dhruxraj/stm32-can-ecu/hardware/gen/fab.py

"""
fab.py - fabrication outputs generated WITHOUT KiCad:
  hardware/fab/gerber/*.g??   RS-274X Gerbers (X2 file attributes), planes and
                              pours included (solid pad connection, no thermals)
  hardware/fab/drill/*.drl     Excellon, separate PTH / NPTH
  hardware/fab/BOM.csv         grouped bill of materials with cost ESTIMATES
  hardware/fab/CPL_top.csv     pick-and-place (top side)
These are PREVIEW outputs for review.  For ordering, re-plot from KiCad
(File > Fabrication Outputs) after filling zones - see docs/MANUFACTURING.md.
"""
import csv
import json
import math
import os
import re

import matplotlib
matplotlib.use("Agg")
import matplotlib.pyplot as plt
from matplotlib.patches import Polygon as MPoly, Circle
from matplotlib.textpath import TextPath
from matplotlib.font_manager import FontProperties

from board import placed_pads_cache, PLACEMENT, outline_polygon, BX1, BY1, BX2, BY2, FOOTPRINTS
from design import PARTS
from lib import rot_pt

ROOT = "/home/claude/stm32-can-ecu/hardware/fab"
GEN = "/home/claude/stm32-can-ecu/hardware/gen"
ZONE_CLR = 0.25
MASK_EXP = 0.05


def gy(y):
    return -y


def c6(v):
    return str(int(round(v * 1e6)))


class Gerber:
    def __init__(self, func, polarity="Positive"):
        self.lines = ["G04 STM32 CAN ECU rev A - generated by hardware/gen/fab.py*",
                      "%TF.GenerationSoftware,custom,can-ecu-gen,1.0*%",
                      "%TF.ProjectId,CAN_ECU,00000000-0000-0000-0000-000000000000,A*%",
                      f"%TF.FileFunction,{func}*%", f"%TF.FilePolarity,{polarity}*%",
                      "%FSLAX46Y46*%", "%MOMM*%", "%LPD*%", "G01*"]
        self.aps = {}
        self.body = []
        self.cur_ap = None
        self.pol = "D"

    def ap(self, kind, *dims):
        key = (kind,) + tuple(round(d, 4) for d in dims)
        if key not in self.aps:
            n = 10 + len(self.aps)
            self.aps[key] = n
        return self.aps[key]

    def _sel(self, n):
        if self.cur_ap != n:
            self.body.append(f"D{n}*")
            self.cur_ap = n

    def polarity(self, p):
        if p != self.pol:
            self.body.append(f"%LP{p}*%")
            self.pol = p

    def flash_circle(self, x, y, d):
        self._sel(self.ap("C", d))
        self.body.append(f"X{c6(x)}Y{c6(gy(y))}D03*")

    def flash_rect(self, x, y, w, h):
        self._sel(self.ap("R", w, h))
        self.body.append(f"X{c6(x)}Y{c6(gy(y))}D03*")

    def flash_obround(self, x, y, w, h):
        self._sel(self.ap("O", w, h))
        self.body.append(f"X{c6(x)}Y{c6(gy(y))}D03*")

    def line(self, a, b, w):
        self._sel(self.ap("C", w))
        self.body.append(f"X{c6(a[0])}Y{c6(gy(a[1]))}D02*")
        self.body.append(f"X{c6(b[0])}Y{c6(gy(b[1]))}D01*")

    def region(self, pts):
        self.body.append("G36*")
        self.body.append(f"X{c6(pts[0][0])}Y{c6(gy(pts[0][1]))}D02*")
        for p in pts[1:] + [pts[0]]:
            self.body.append(f"X{c6(p[0])}Y{c6(gy(p[1]))}D01*")
        self.body.append("G37*")

    def save(self, path):
        out = list(self.lines)
        for key, n in sorted(self.aps.items(), key=lambda x: x[1]):
            kind = key[0]
            if kind == "C":
                out.append(f"%ADD{n}C,{key[1]:.4f}*%")
            elif kind == "R":
                out.append(f"%ADD{n}R,{key[1]:.4f}X{key[2]:.4f}*%")
            elif kind == "O":
                out.append(f"%ADD{n}O,{key[1]:.4f}X{key[2]:.4f}*%")
        out += self.body
        if self.pol != "D":
            out.append("%LPD*%")
        out.append("M02*")
        open(path, "w").write("\n".join(out) + "\n")


def rounded_rect_pts(cx, cy, w, h, r, rot, n=4):
    """polygon of a (rounded) rectangle, rotation multiple of 90."""
    if rot % 180 == 90:
        w, h = h, w
    r = min(r, w / 2, h / 2)
    pts = []
    corners = [(cx + w / 2 - r, cy - h / 2 + r, -90, 0), (cx + w / 2 - r, cy + h / 2 - r, 0, 90),
               (cx - w / 2 + r, cy + h / 2 - r, 90, 180), (cx - w / 2 + r, cy - h / 2 + r, 180, 270)]
    for x, y, a0, a1 in corners:
        if r <= 1e-6:
            pts.append((x, y))
            continue
        for i in range(n + 1):
            a = math.radians(a0 + (a1 - a0) * i / n)
            pts.append((x + r * math.cos(a), y + r * math.sin(a)))
    return pts


def draw_pad(g, p, grow=0.0):
    """draw pad copper (optionally grown by `grow`) with the current polarity."""
    w, h = p.w + 2 * grow, p.h + 2 * grow
    if p.shape == "circle":
        g.flash_circle(p.x, p.y, w)
    elif p.shape == "oval":
        if p.rot % 180 == 90:
            w, h = h, w
        g.flash_obround(p.x, p.y, w, h)
    elif p.shape == "rect" and grow == 0:
        if p.rot % 180 == 90:
            w, h = h, w
        g.flash_rect(p.x, p.y, w, h)
    else:
        r = (min(p.w, p.h) * p.pad.rratio if p.shape == "roundrect" else 0.0) + grow
        g.region(rounded_rect_pts(p.x, p.y, w, h, r, p.rot))


def load_routes():
    return json.load(open(os.path.join(GEN, "routes.json")))


def copper_layer(layer, R, pour_net=None, plane=False):
    func = {"F.Cu": "Copper,L1,Top", "In1.Cu": "Copper,L2,Inr", "In2.Cu": "Copper,L3,Inr",
            "B.Cu": "Copper,L4,Bot"}[layer]
    g = Gerber(func)
    pads = [p for p in placed_pads_cache() if layer in p.layers]
    tracks = [t for t in R["tracks"] if t["layer"] == layer]
    vias = R["vias"]
    npth = [p for p in placed_pads_cache() if p.kind == "np_thru_hole"]
    if pour_net:
        g.region(outline_polygon(0.3, 8))
        g.polarity("C")
        for p in pads:
            if p.net != pour_net:
                draw_pad(g, p, ZONE_CLR)
        for t in tracks:
            if t["net"] != pour_net:
                g.line(t["a"], t["b"], t["w"] + 2 * ZONE_CLR)
        for v in vias:
            if v["net"] != pour_net:
                g.flash_circle(v["at"][0], v["at"][1], v["size"] + 2 * ZONE_CLR)
        for p in npth:
            g.flash_circle(p.x, p.y, p.drill + 2 * 0.5)
        g.polarity("D")
    if not plane:
        for t in tracks:
            g.line(t["a"], t["b"], t["w"])
    for p in pads:
        if plane and p.net != pour_net:
            continue            # inner layers: non-plane pads have no copper (unused pads removed)
        draw_pad(g, p)
    for v in vias:
        if plane and v["net"] != pour_net:
            continue
        g.flash_circle(v["at"][0], v["at"][1], v["size"])
    return g


def mask_layer(side, R):
    g = Gerber("Soldermask,Top" if side == "F" else "Soldermask,Bot", "Negative")
    for p in placed_pads_cache():
        if p.kind == "np_thru_hole":
            g.flash_circle(p.x, p.y, p.drill + 0.1)
            continue
        if side == "B" and p.kind != "thru_hole":
            continue
        draw_pad(g, p, MASK_EXP)
    return g            # vias are tented


def paste_layer(R):
    g = Gerber("Paste,Top", "Positive")
    for p in placed_pads_cache():
        if p.kind == "smd":
            draw_pad(g, p)
    return g


FONT = FontProperties(family="DejaVu Sans")


def text_polys(s, x, y, size, rot):
    tp = TextPath((0, 0), s, size=size * 1.35, prop=FONT)
    polys = tp.to_polygons()
    if not polys:
        return []
    xs = [p[0] for poly in polys for p in poly]
    ys = [p[1] for poly in polys for p in poly]
    cx, cy = (min(xs) + max(xs)) / 2, (min(ys) + max(ys)) / 2
    out = []
    for poly in polys:
        pts = []
        for (px, py) in poly:
            lx, ly = px - cx, -(py - cy)          # text y-up -> board y-down
            dx, dy = rot_pt(lx, ly, rot)
            pts.append((x + dx, y + dy))
        area = sum(pts[i][0] * pts[(i + 1) % len(pts)][1] - pts[(i + 1) % len(pts)][0] * pts[i][1]
                   for i in range(len(pts))) / 2
        out.append((pts, area))
    return out


def silk_layer(meta):
    from write_kicad import BOARD_TEXT
    g = Gerber("Legend,Top")
    pads = placed_pads_cache()
    for ref, part in PARTS.items():
        fx, fy, frot = PLACEMENT[ref]
        f = FOOTPRINTS[part.fp]
        for gr in f.gfx:
            if gr[1] != "F.SilkS":
                continue
            if gr[0] == "line":
                _, L, x1, y1, x2, y2, w = gr
                a = rot_pt(x1, y1, frot); b = rot_pt(x2, y2, frot)
                g.line((fx + a[0], fy + a[1]), (fx + b[0], fy + b[1]), w)
            else:
                _, L, cx, cy, r, w = gr
                c = rot_pt(cx, cy, frot)
                n = 36
                pts = [(fx + c[0] + r * math.cos(2 * math.pi * i / n), fy + c[1] + r * math.sin(2 * math.pi * i / n))
                       for i in range(n + 1)]
                for a, b in zip(pts[:-1], pts[1:]):
                    g.line(a, b, w)
    texts = []
    for ref, s in meta["silk"].items():
        if s:
            texts.append((ref, s[0], s[1], 0.8, s[2]))
    for (t, x, y, sz, rot) in BOARD_TEXT:
        texts.append((t, x, y, sz, rot))
    for (t, x, y, sz, rot) in texts:
        polys = text_polys(t, x, y, sz, rot)
        # matplotlib glyph outer contours come out with positive area in board
        # (y-down) coordinates, counter/hole contours negative
        outer = [p for p, a in polys if a > 0]
        holes = [p for p, a in polys if a <= 0]
        for p in outer:
            g.region(p)
            for a, b in zip(p, p[1:] + p[:1]):      # embolden: KiCad plots 0.15 mm strokes
                g.line(a, b, 0.07)
        if holes:
            g.polarity("C")
            for p in holes:
                g.region(p)
            g.polarity("D")
    # clip silk from exposed pads (as KiCad does)
    g.polarity("C")
    for p in pads:
        if p.kind != "np_thru_hole":
            draw_pad(g, p, MASK_EXP + 0.05)
    g.polarity("D")
    return g


def edge_layer():
    g = Gerber("Profile,NP")
    pts = outline_polygon(0.0, 16)
    for a, b in zip(pts, pts[1:] + pts[:1]):
        g.line(a, b, 0.1)
    return g


def drill_files(R, d):
    pth, npth = {}, {}
    for p in placed_pads_cache():
        if p.drill:
            (npth if p.kind == "np_thru_hole" else pth).setdefault(p.drill, []).append((p.x, p.y))
    for v in R["vias"]:
        pth.setdefault(v["drill"], []).append(tuple(v["at"]))
    for name, tools, plated in [("CAN_ECU-PTH.drl", pth, True), ("CAN_ECU-NPTH.drl", npth, False)]:
        out = ["M48", "; DRILL file - STM32 CAN ECU rev A - generated by hardware/gen/fab.py",
               f"; #@! TF.FileFunction,{'Plated,1,4,PTH' if plated else 'NonPlated,1,4,NPTH'}",
               "FMAT,2", "METRIC,TZ"]
        tl = sorted(tools)
        for i, dia in enumerate(tl):
            out.append(f"T{i + 1}C{dia:.3f}")
        out += ["%", "G90", "G05"]
        for i, dia in enumerate(tl):
            out.append(f"T{i + 1}")
            for x, y in tools[dia]:
                out.append(f"X{x:.3f}Y{gy(y):.3f}")
        out += ["T0", "M30"]
        open(os.path.join(d, name), "w").write("\n".join(out) + "\n")
    return pth, npth


# ------------------------------------------------------------------ BOM / CPL
COST = [  # (match on MPN/value substring, est. unit cost USD at qty 10) - ROUGH estimates only
    ("STM32G431CBT6", 4.60), ("TJA1051T", 1.10), ("LSM6DS3TR-C", 2.40), ("R-78E5.0", 3.60),
    ("AP2112K", 0.35), ("SMBJ18A", 0.25), ("SS34", 0.15), ("PTC", 0.35), ("PESD1CAN", 0.25),
    ("8MHz", 0.40), ("1729128", 0.70), ("1729131", 1.00), ("1x6", 0.25), ("2x5", 0.35),
    ("2x2", 0.30), ("tactile", 0.15), ("47uF", 0.20), ("10uF 50V", 0.35), ("10uF", 0.08),
    ("4.7uF", 0.06), ("1uF", 0.03), ("60R4", 0.04), ("LED", 0.05), ("600R", 0.05),
    ("15pF", 0.03), ("4.7nF", 0.03), ("100nF", 0.02), ("R", 0.01),
]


def est_cost(p):
    key = f"{p.mpn} {p.value} {p.sym}"
    for k, c in COST:
        if k in key:
            return c
    return 0.0


def bom(d):
    groups = {}
    for p in PARTS.values():
        if p.sym in ("MountingHole", "TestPoint", "SolderJumper_2_Open"):
            continue
        k = (p.value, p.fp, p.mpn)
        groups.setdefault(k, []).append(p)
    rows = []
    total = 0.0
    for i, ((val, fp, mpn), ps) in enumerate(sorted(groups.items(), key=lambda x: _refkey(x[1][0].ref))):
        refs = sorted((p.ref for p in ps), key=_refkey)
        uc = est_cost(ps[0])
        total += uc * len(ps)
        f = FOOTPRINTS[fp]
        descs = "; ".join(sorted({p.desc for p in ps}))
        spec = mpn or f"generic {val}, {fp.split('_')[1] if fp[:2] in ('R_', 'C_', 'L_') else fp}"
        rows.append([i + 1, len(ps), " ".join(refs), val, fp, f.std, spec, ps[0].mfr, descs,
                     "THT" if f.attr == "through_hole" else "SMD", f"{uc:.2f}", f"{uc * len(ps):.2f}"])
    with open(os.path.join(d, "BOM.csv"), "w", newline="") as fh:
        w = csv.writer(fh)
        w.writerow(["Item", "Qty", "References", "Value", "Footprint (project lib)", "Equivalent KiCad std footprint",
                    "MPN / specification", "Manufacturer", "Description", "Mount", "Est. unit USD", "Est. ext. USD"])
        w.writerows(rows)
        w.writerow([])
        w.writerow(["", "", "", "", "", "", "", "", "Estimated component total per board (qty-10 pricing, "
                    "ROUGH ESTIMATE - check distributor)", "", "", f"{total:.2f}"])
        w.writerow(["", "", "JP1 JP3 JP4", "Solder jumpers", "", "", "PCB feature - no part", "", "", "", "", ""])
        w.writerow(["", "", "TP1-TP8", "Test pads", "", "", "PCB feature - no part", "", "", "", "", ""])
        w.writerow(["", "", "H1-H4", "M3 mounting holes", "", "", "PCB feature - no part", "", "", "", "", ""])
    return rows, total


def _refkey(r):
    m = re.match(r"([A-Z]+)(\d+)", r)
    return (m.group(1), int(m.group(2)))


def cpl(d):
    with open(os.path.join(d, "CPL_top.csv"), "w", newline="") as fh:
        w = csv.writer(fh)
        w.writerow(["Designator", "Mid X (mm)", "Mid Y (mm)", "Rotation (deg, CCW)", "Layer", "Mount", "Value",
                    "Footprint"])
        for ref in sorted(PARTS, key=_refkey):
            p = PARTS[ref]
            f = FOOTPRINTS[p.fp]
            if f.attr == "exclude" or p.sym in ("TestPoint", "SolderJumper_2_Open"):
                continue
            x, y, r = PLACEMENT[ref]
            w.writerow([ref, f"{x - BX1:.3f}", f"{BY2 - y:.3f}", r, "Top",
                        "THT" if f.attr == "through_hole" else "SMD", p.value, p.fp])


# ------------------------------------------------------------------ gerber re-render (independent check)
def render_gerber(path, ax, color, bg):
    txt = open(path).read()
    aps = {}
    for m in re.finditer(r"%ADD(\d+)([CRO]),([\d.]+)(?:X([\d.]+))?\*%", txt):
        aps[int(m.group(1))] = (m.group(2), float(m.group(3)), float(m.group(4) or 0))
    cur = None; x = y = 0.0; pol = "D"; region = None
    col = lambda: color if pol == "D" else bg
    for cmd in re.findall(r"%[^%]*%|[^*%\n]+\*", txt):
        cmd = cmd.strip()
        if cmd.startswith("%LP"):
            pol = cmd[3]; continue
        if cmd.startswith("%"):
            continue
        cmd = cmd.rstrip("*")
        if cmd == "G36":
            region = []; continue
        if cmd == "G37":
            ax.add_patch(MPoly(region, closed=True, fc=col(), ec="none")); region = None; continue
        m = re.match(r"^D(\d+)$", cmd)
        if m and int(m.group(1)) >= 10:
            cur = aps[int(m.group(1))]; continue
        m = re.match(r"^X(-?\d+)Y(-?\d+)D0([123])$", cmd)
        if not m:
            continue
        nx, ny, op = int(m.group(1)) / 1e6, -int(m.group(2)) / 1e6, m.group(3)
        if region is not None:
            region.append((nx, ny))
        elif op == "1":
            hw = cur[1] / 2
            L = math.hypot(nx - x, ny - y) or 1e-9
            px, py = -(ny - y) / L * hw, (nx - x) / L * hw
            ax.add_patch(MPoly([(x + px, y + py), (nx + px, ny + py), (nx - px, ny - py), (x - px, y - py)],
                               closed=True, fc=col(), ec="none"))
            ax.add_patch(Circle((x, y), hw, fc=col(), ec="none"))
            ax.add_patch(Circle((nx, ny), hw, fc=col(), ec="none"))
        elif op == "3":
            k, a, b = cur
            if k == "C" or (k == "O" and abs(a - b) < 1e-6):
                ax.add_patch(Circle((nx, ny), a / 2, fc=col(), ec="none"))
            elif k == "O":
                r = min(a, b) / 2
                ax.add_patch(Circle((nx - (a / 2 - r), ny - (b / 2 - r)), r, fc=col(), ec="none"))
                ax.add_patch(Circle((nx + (a / 2 - r), ny + (b / 2 - r)), r, fc=col(), ec="none"))
                w2, h2 = (a / 2 - r, r) if a > b else (r, b / 2 - r)
                ax.add_patch(MPoly([(nx - w2, ny - h2), (nx + w2, ny - h2), (nx + w2, ny + h2), (nx - w2, ny + h2)],
                                   closed=True, fc=col(), ec="none"))
            else:
                ax.add_patch(MPoly([(nx - a / 2, ny - b / 2), (nx + a / 2, ny - b / 2), (nx + a / 2, ny + b / 2),
                                    (nx - a / 2, ny + b / 2)], closed=True, fc=col(), ec="none"))
        x, y = nx, ny


_scale = [1.0]


def preview(gdir, out_png, files, title):
    fig, ax = plt.subplots(figsize=(12, 9), dpi=100)
    ax.set_xlim(BX1 - 1, BX2 + 1); ax.set_ylim(BY2 + 1, BY1 - 1); ax.set_aspect("equal")
    fig.canvas.draw()
    # points per mm for track widths
    bb = ax.get_window_extent()
    _scale[0] = (bb.width / (BX2 - BX1 + 2)) / (fig.dpi / 25.4 * 1.0) / 1.0
    ax.set_facecolor("#1a1a1a")
    for fn, colr, bg in files:
        render_gerber(os.path.join(gdir, fn), ax, colr, bg)
    ax.set_title(title)
    fig.savefig(out_png, bbox_inches="tight")
    plt.close(fig)


def main():
    R = load_routes()
    meta = json.load(open(os.path.join(GEN, "layout_meta.json")))
    gd = os.path.join(ROOT, "gerber"); dd = os.path.join(ROOT, "drill")
    os.makedirs(gd, exist_ok=True); os.makedirs(dd, exist_ok=True)
    copper_layer("F.Cu", R, pour_net="GND").save(os.path.join(gd, "CAN_ECU-F_Cu.gtl"))
    copper_layer("In1.Cu", R, pour_net="GND", plane=True).save(os.path.join(gd, "CAN_ECU-In1_Cu.g2"))
    copper_layer("In2.Cu", R, pour_net="+3V3", plane=True).save(os.path.join(gd, "CAN_ECU-In2_Cu.g3"))
    copper_layer("B.Cu", R, pour_net="GND").save(os.path.join(gd, "CAN_ECU-B_Cu.gbl"))
    mask_layer("F", R).save(os.path.join(gd, "CAN_ECU-F_Mask.gts"))
    mask_layer("B", R).save(os.path.join(gd, "CAN_ECU-B_Mask.gbs"))
    paste_layer(R).save(os.path.join(gd, "CAN_ECU-F_Paste.gtp"))
    silk_layer(meta).save(os.path.join(gd, "CAN_ECU-F_Silkscreen.gto"))
    edge_layer().save(os.path.join(gd, "CAN_ECU-Edge_Cuts.gm1"))
    pth, npth = drill_files(R, dd)
    rows, total = bom(ROOT)
    cpl(ROOT)
    img = "/home/claude/stm32-can-ecu/docs/img"
    os.makedirs(img, exist_ok=True)
    preview(gd, os.path.join(img, "gerber_top.png"),
            [("CAN_ECU-F_Cu.gtl", "#c87533", "#1a1a1a"), ("CAN_ECU-F_Silkscreen.gto", "#f0f0f0", "#c87533"),
             ("CAN_ECU-Edge_Cuts.gm1", "yellow", "k")], "Gerber re-render: F.Cu (copper) + F.Silkscreen")
    preview(gd, os.path.join(img, "gerber_bottom.png"),
            [("CAN_ECU-B_Cu.gbl", "#3a7bd5", "#1a1a1a"), ("CAN_ECU-Edge_Cuts.gm1", "yellow", "k")],
            "Gerber re-render: B.Cu (viewed from top)")
    preview(gd, os.path.join(img, "gerber_in1_gnd.png"),
            [("CAN_ECU-In1_Cu.g2", "#9a9a30", "#1a1a1a"), ("CAN_ECU-Edge_Cuts.gm1", "yellow", "k")],
            "Gerber re-render: In1.Cu GND plane")
    preview(gd, os.path.join(img, "gerber_in2_3v3.png"),
            [("CAN_ECU-In2_Cu.g3", "#a060a0", "#1a1a1a"), ("CAN_ECU-Edge_Cuts.gm1", "yellow", "k")],
            "Gerber re-render: In2.Cu +3V3 plane")
    print("BOM lines:", len(rows), "est. component cost USD:", round(total, 2))
    print("PTH tools:", {k: len(v) for k, v in pth.items()}, "NPTH:", {k: len(v) for k, v in npth.items()})


if __name__ == "__main__":
    main()
